lzha97/EZBreathe/Assem13-CADfiles/37d-gearmotor-19-30-encoder.SLDPRT

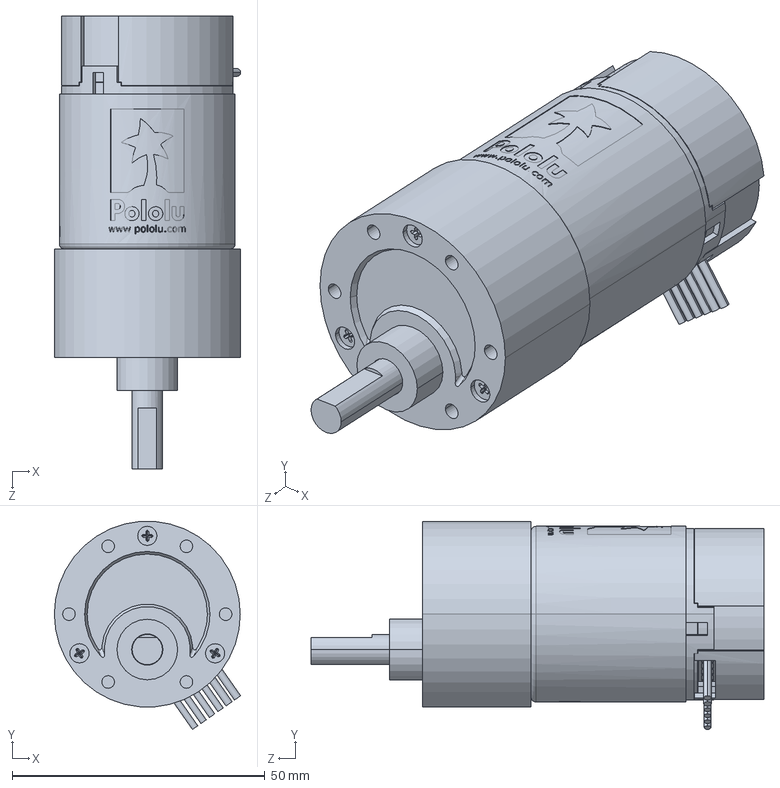
[picture p29: CAD file, 2020-04-07]
Assem13-CADfiles/37d-gearmotor-19-30-encoder.SLDPRT
36.9 x 41.2 x 89.6 mm
