lzha97/EZBreathe/Assem13-CADfiles/string disk.SLDPRT

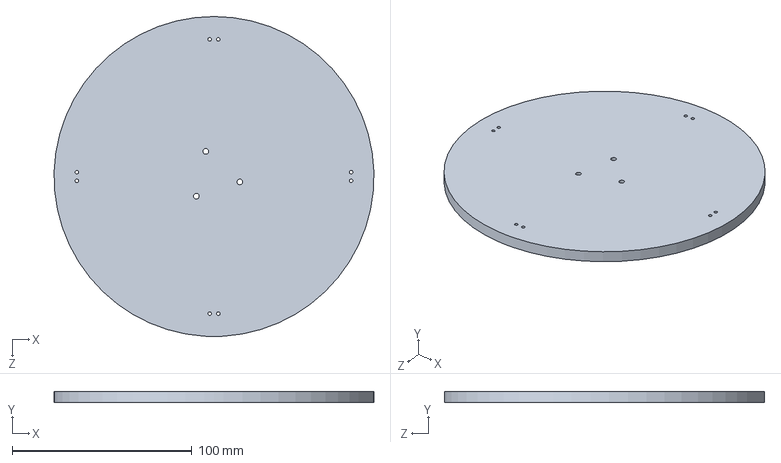
[picture p30: CAD file, 2020-04-07]
Assem13-CADfiles/string disk.SLDPRT
177.7 x 6.35 x 177.8 mm
