lzha97/EZBreathe/Assem13-CADfiles/ambubag part.SLDPRT

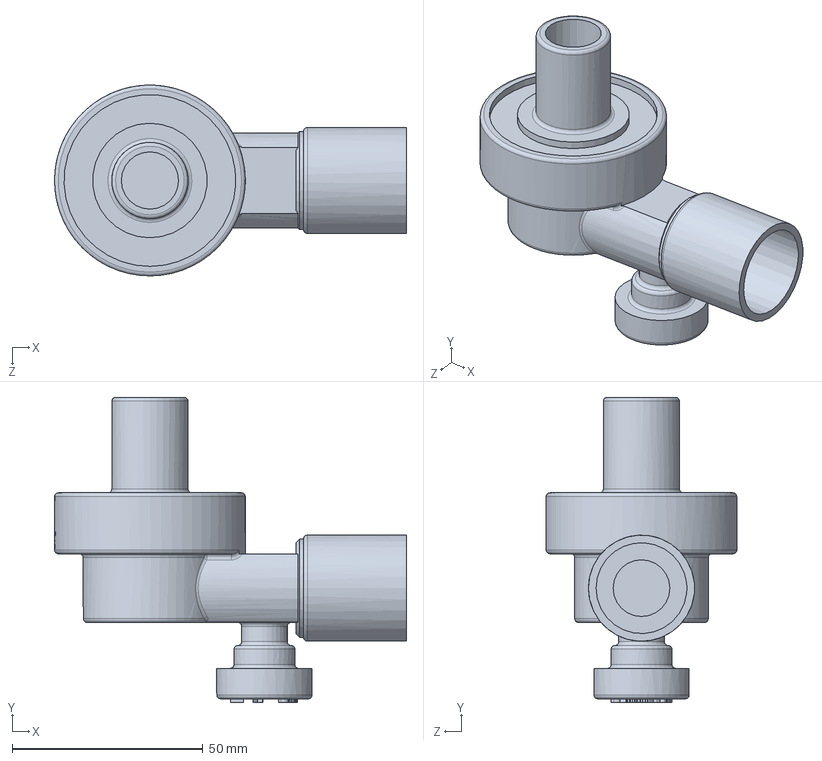
[picture p31: CAD file, 2020-04-07]
Assem13-CADfiles/ambubag part.SLDPRT
92.2 x 80.0 x 50.0 mm
