lzha97/EZBreathe/Assem13-CADfiles/squeezer.SLDPRT

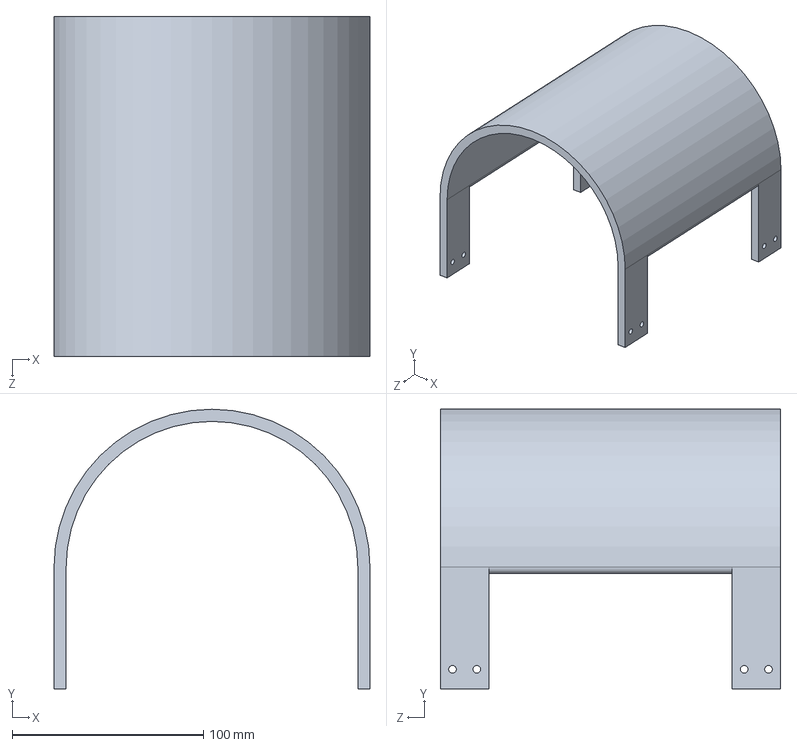
[picture p33: CAD file, 2020-04-07]
Assem13-CADfiles/squeezer.SLDPRT
165.1 x 146.0 x 177.8 mm
