lzha97/EZBreathe/Assem13-CADfiles/long wall.SLDPRT

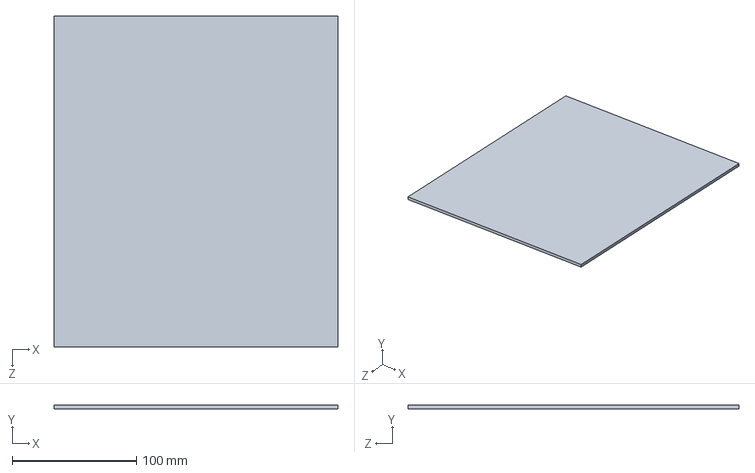
[picture p34: CAD file, 2020-04-07]
Assem13-CADfiles/long wall.SLDPRT
228.6 x 3.17 x 266.7 mm
