lzha97/EZBreathe/Assem13-CADfiles/shelf.SLDPRT

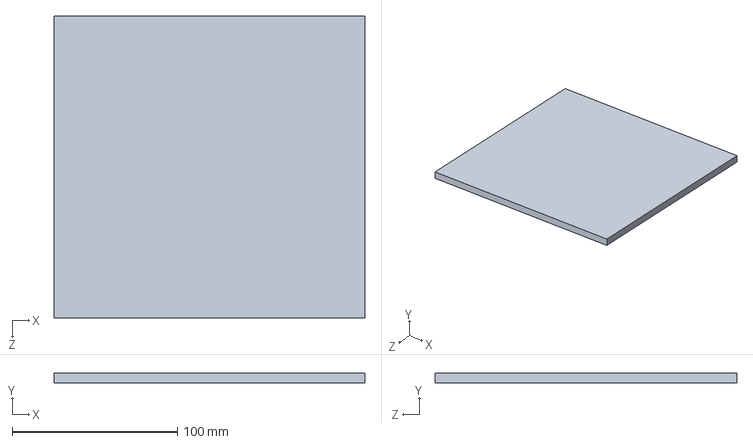
[picture p35: CAD file, 2020-04-07]
Assem13-CADfiles/shelf.SLDPRT
188.5 x 6.35 x 182.9 mm
