lzha97/EZBreathe/Assem13-CADfiles/platform.SLDPRT

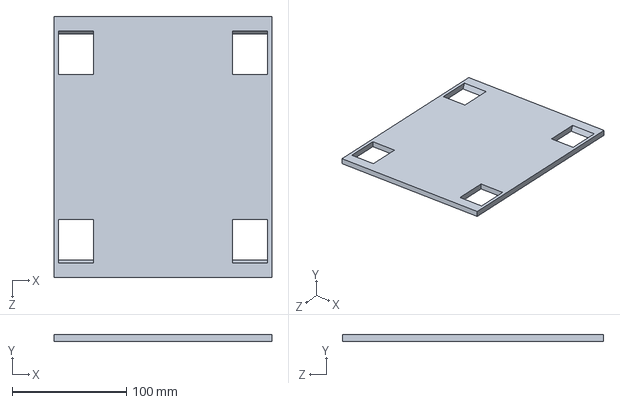
[picture p36: CAD file, 2020-04-07]
Assem13-CADfiles/platform.SLDPRT
190.5 x 6.35 x 228.6 mm
