lzha97/EZBreathe/Assem13-CADfiles/SEN-09376 Force Sensing Resistor.SLDPRT

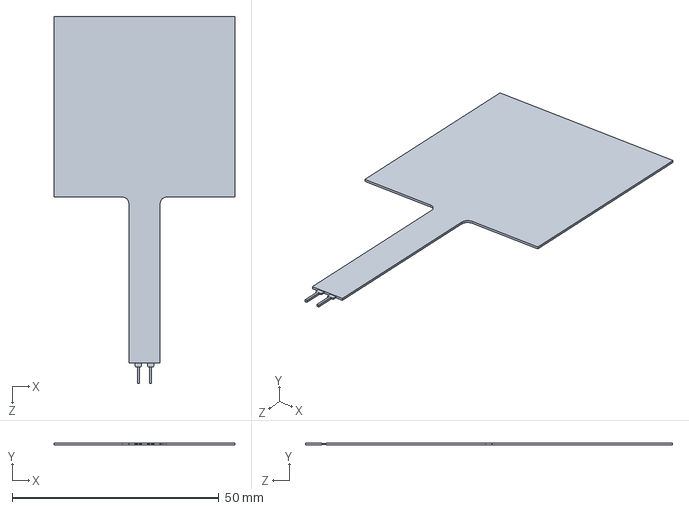
[picture p37: CAD file, 2020-04-07]
Assem13-CADfiles/SEN-09376 Force Sensing Resistor.SLDPRT
43.7 x 0.465 x 88.8 mm
