lzha97/EZBreathe/Assem13-CADfiles/Hinge fin.sldprt

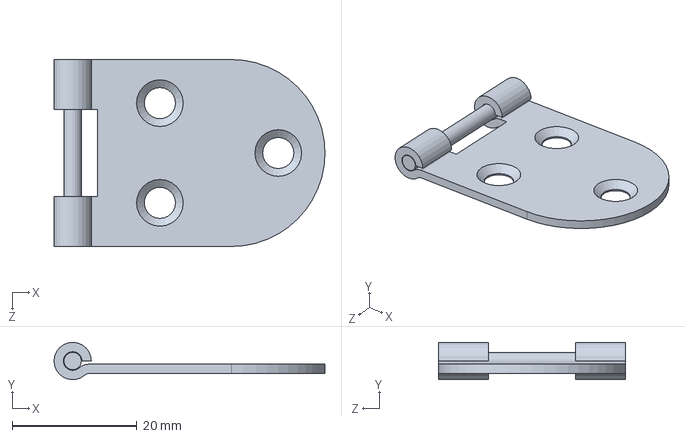
[picture p38: CAD file, 2020-04-07]
Assem13-CADfiles/Hinge fin.sldprt
43.5 x 6.00 x 30.0 mm
