lzha97/EZBreathe/Assem13-CADfiles/tower - h.SLDPRT

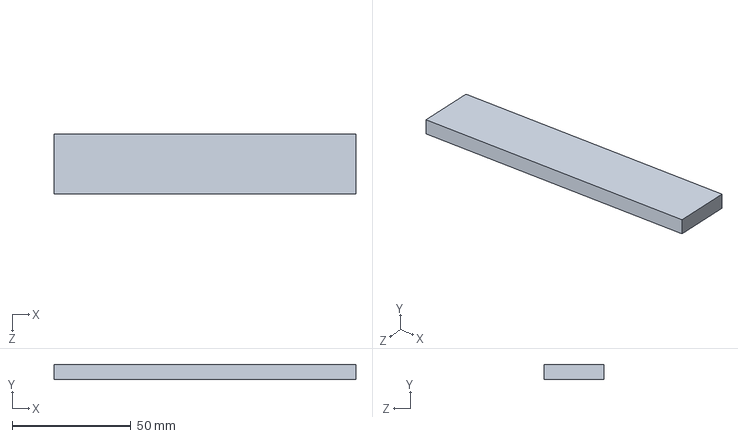
[picture p39: CAD file, 2020-04-07]
Assem13-CADfiles/tower - h.SLDPRT
127.0 x 6.35 x 25.4 mm
