lzha97/EZBreathe/Assem13-CADfiles/motor bracket.SLDPRT

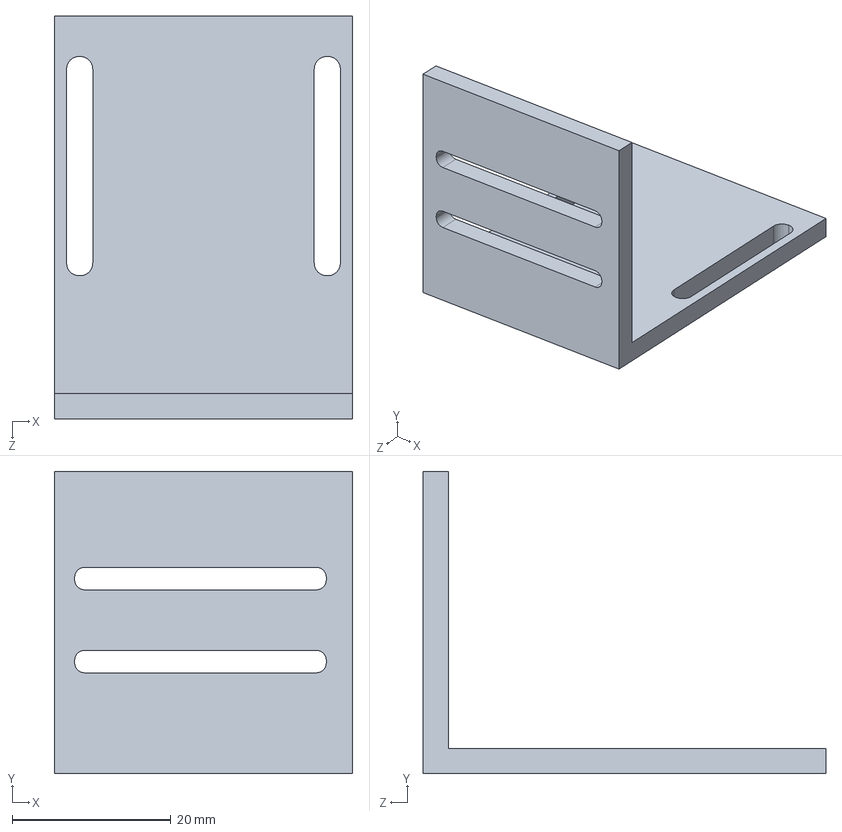
[picture p40: CAD file, 2020-04-07]
Assem13-CADfiles/motor bracket.SLDPRT
37.6 x 38.1 x 50.8 mm
