lzha97/EZBreathe/Assem13-CADfiles/pololu-stamped-aluminum-L-bracket-for-37d-mm-metal-gearmotors.SLDPRT

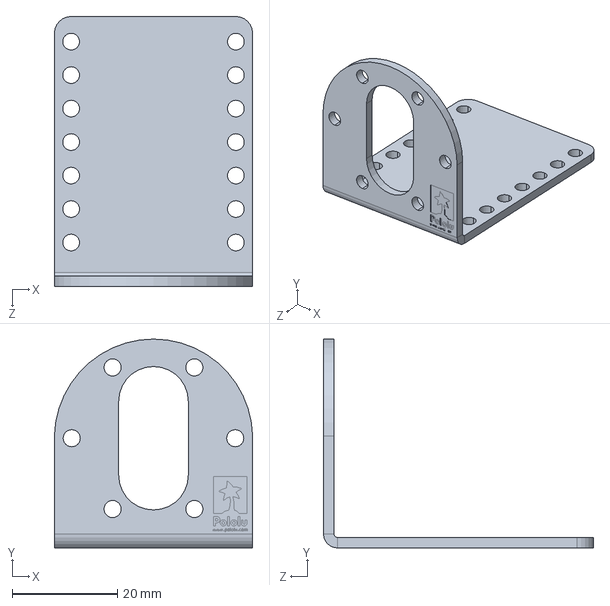
[picture p41: CAD file, 2020-04-07]
Assem13-CADfiles/pololu-stamped-aluminum-L-bracket-for-37d-mm-metal-gearmotors.SLDPRT
37.6 x 39.6 x 51.2 mm
